MarthCage/FdD_Equipo_09/Proyecto/MóduloMecánico/Certificados ONSHAPE/Angel Valverde Paucarmayta/Certificados_Angel_Valverde_Paucarmayta.pdf

Onshape Fundamentals

April 28, 2026

Angel Valverde

Angel Valverde

April 28, 2026

Introduction to Drawings

Angel Valverde

Introduction to Part Studios

April 28, 2026

Angel Valverde

CAD Basics

April 28, 2026

Angel Valverde

Introduction to Sketching

April 28, 2026

Angel Valverde

April 28, 2026

Detailed Drawings

Angel Valverde

April 28, 2026

Introduction to Onshape Assemblies

Angel Gabriel Valverde Paucarmayta

Advanced Onshape Assemblies

May 19, 2026
