MarthCage/FdD_Equipo_09/Proyecto/MóduloMecánico/Certificados ONSHAPE/Martha Medina Rojas/Certificados_Martha_Medina_Rojas.pdf

Onshape Fundamentals

April 28, 2026

Martha Medina

Martha Medina

Introduction to Sketching

April 28, 2026

Martha Medina

Introduction to Part Studios

April 28, 2026

Martha Medina

CAD Basics

April 28, 2026

Martha Medina

April 28, 2026

Introduction to Drawings

Martha Medina

April 28, 2026

Detailed Drawings

Martha Medina

April 28, 2026

Introduction to Onshape Assemblies

Martha Medina

Advanced Onshape Assemblies

May 19, 2026
