MarthCage/FdD_Equipo_09/Recursos/Productos comerciales/Guardian 3.pdf

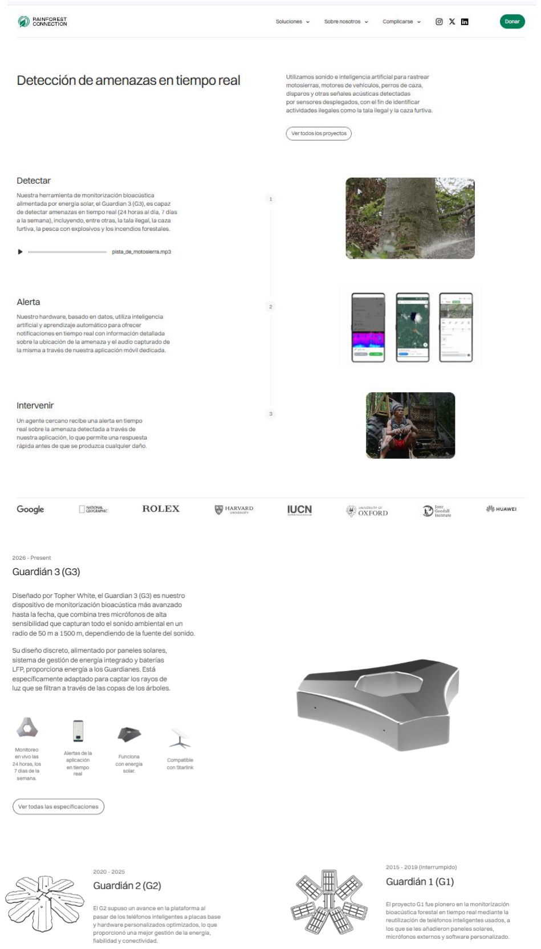
[picture p41: page 1]
