MarthCage/FdD_Equipo_09/Proyecto/MóduloElectrónico/V3.0/Esquemático 3.0 (2).pdf

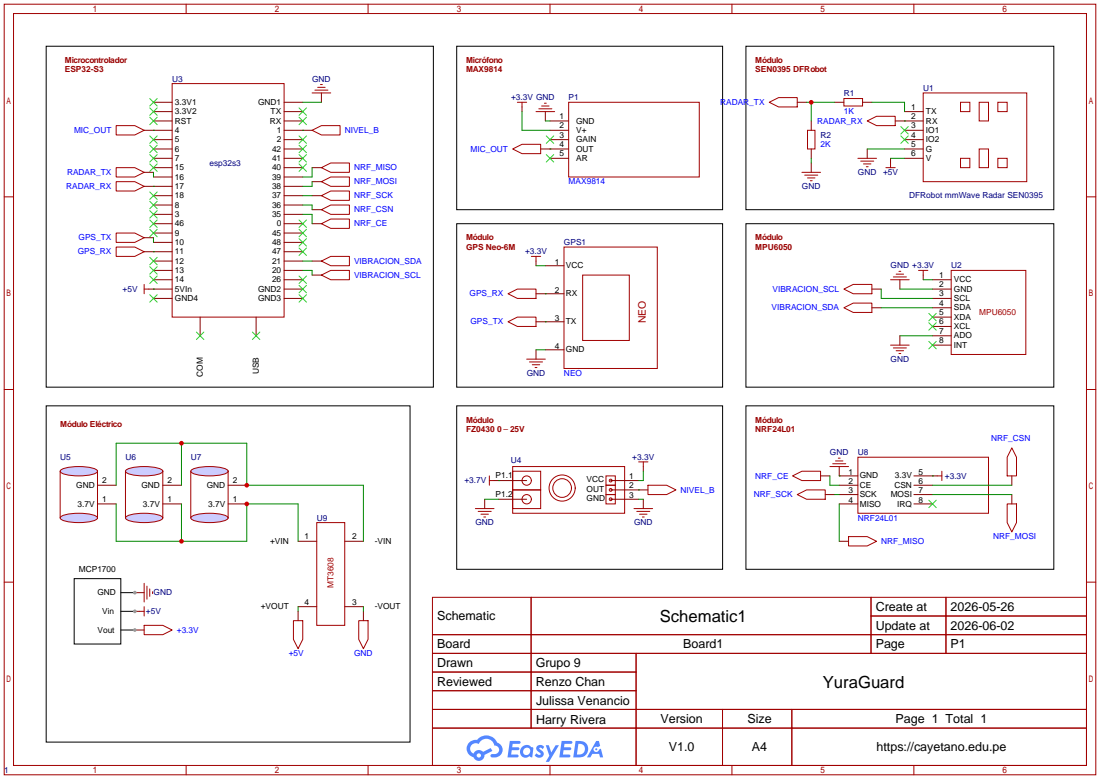
[picture p54: page 1]

Schematic | Schematic1 | Create at | 2026-05-26

Update at | 2026-06-02

Board | Board1 | Page | P1
Drawn | Grupo 9 | YuraGuard
Reviewed | Renzo Chan

Julissa Venancio
Harry Rivera | Version | Size | Page 1 Total 1

V1.0 | A4 | https://cayetano.edu.pe
