MarthCage/FdD_Equipo_09/Proyecto/MóduloMecánico/v2.0/Onshape/planos/PCB1_plano.pdf

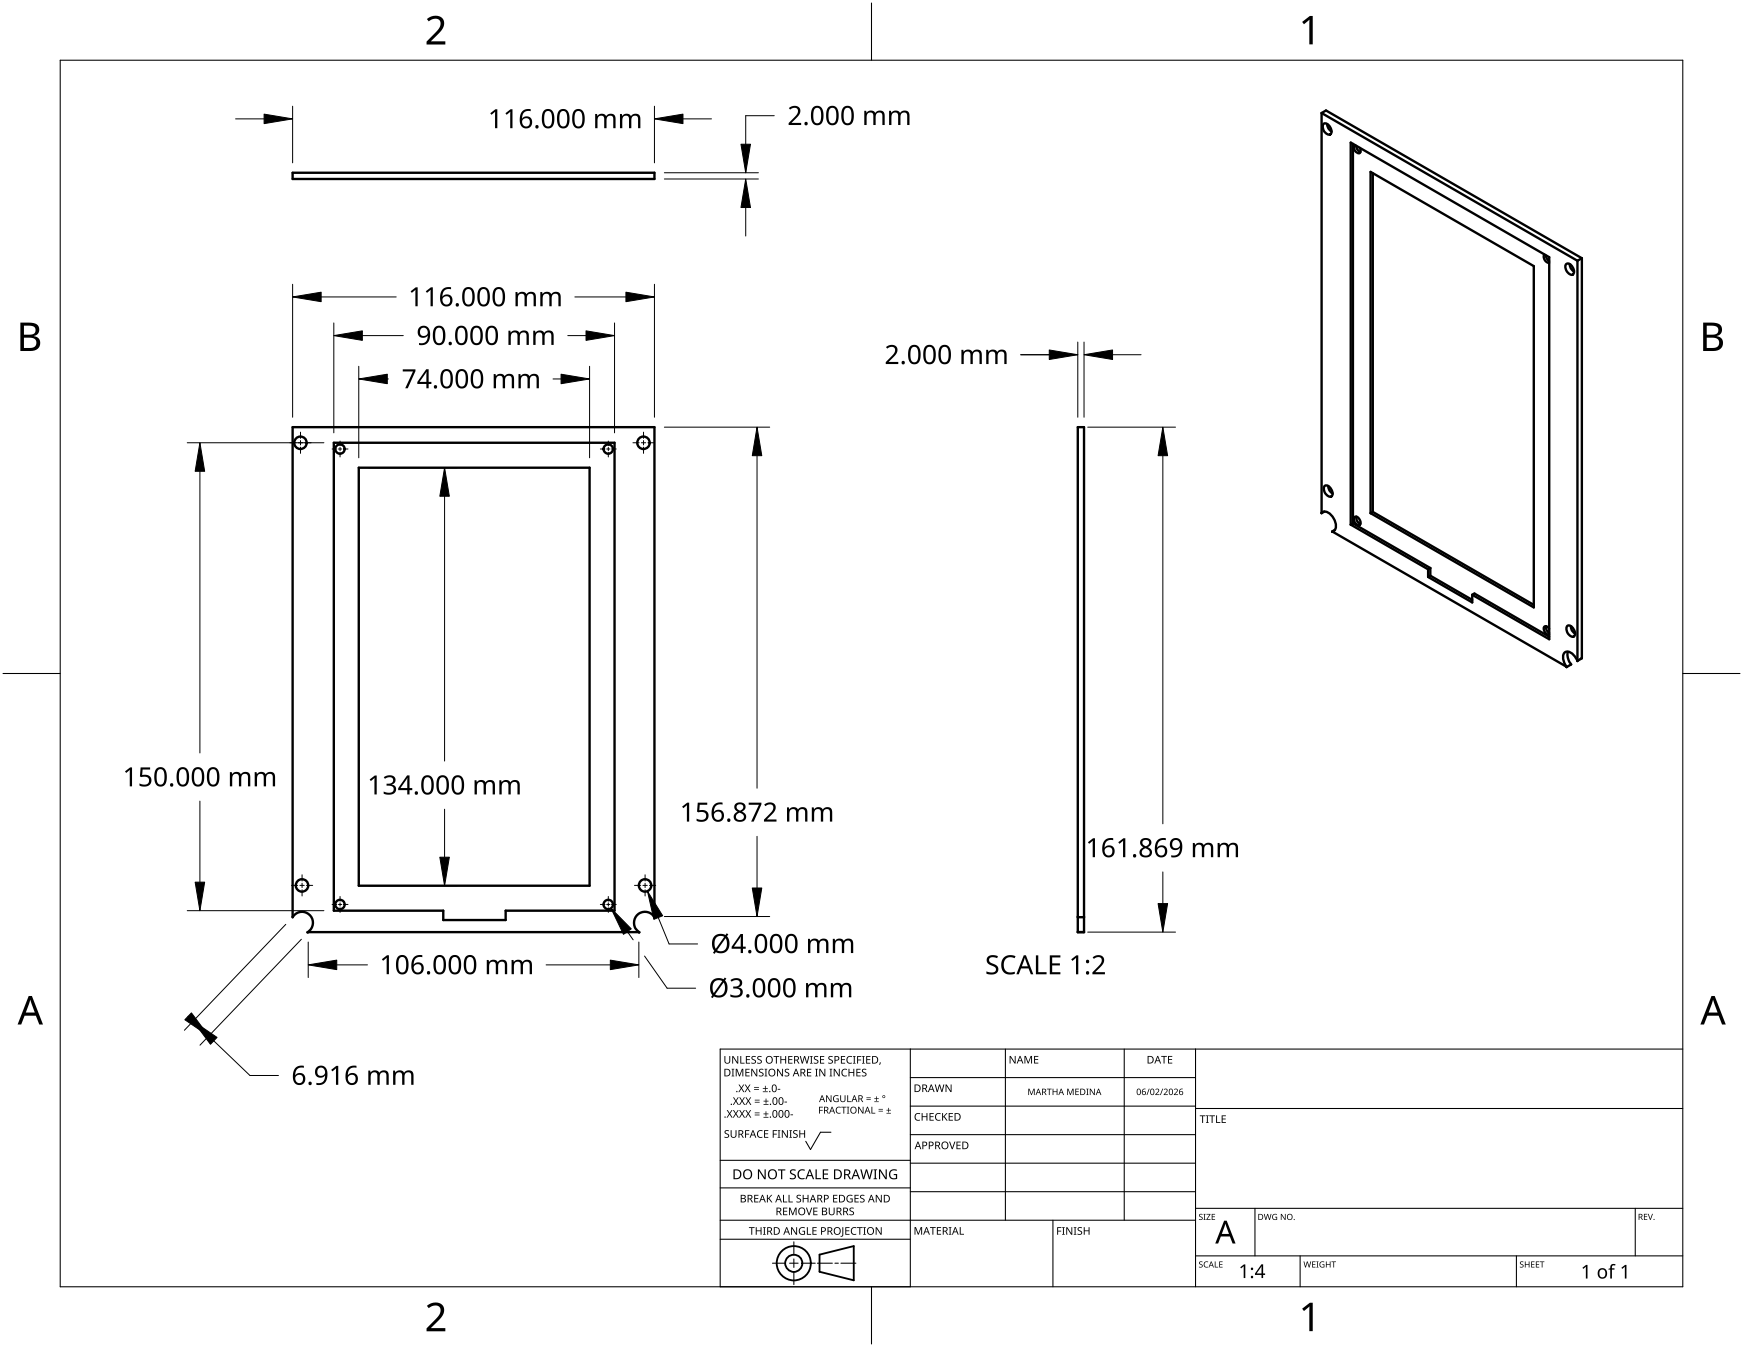
[picture p105: page 1]
