MarthCage/FdD_Equipo_09/Proyecto/MóduloMecánico/v2.0/Onshape/planos/PCB2_plano.pdf

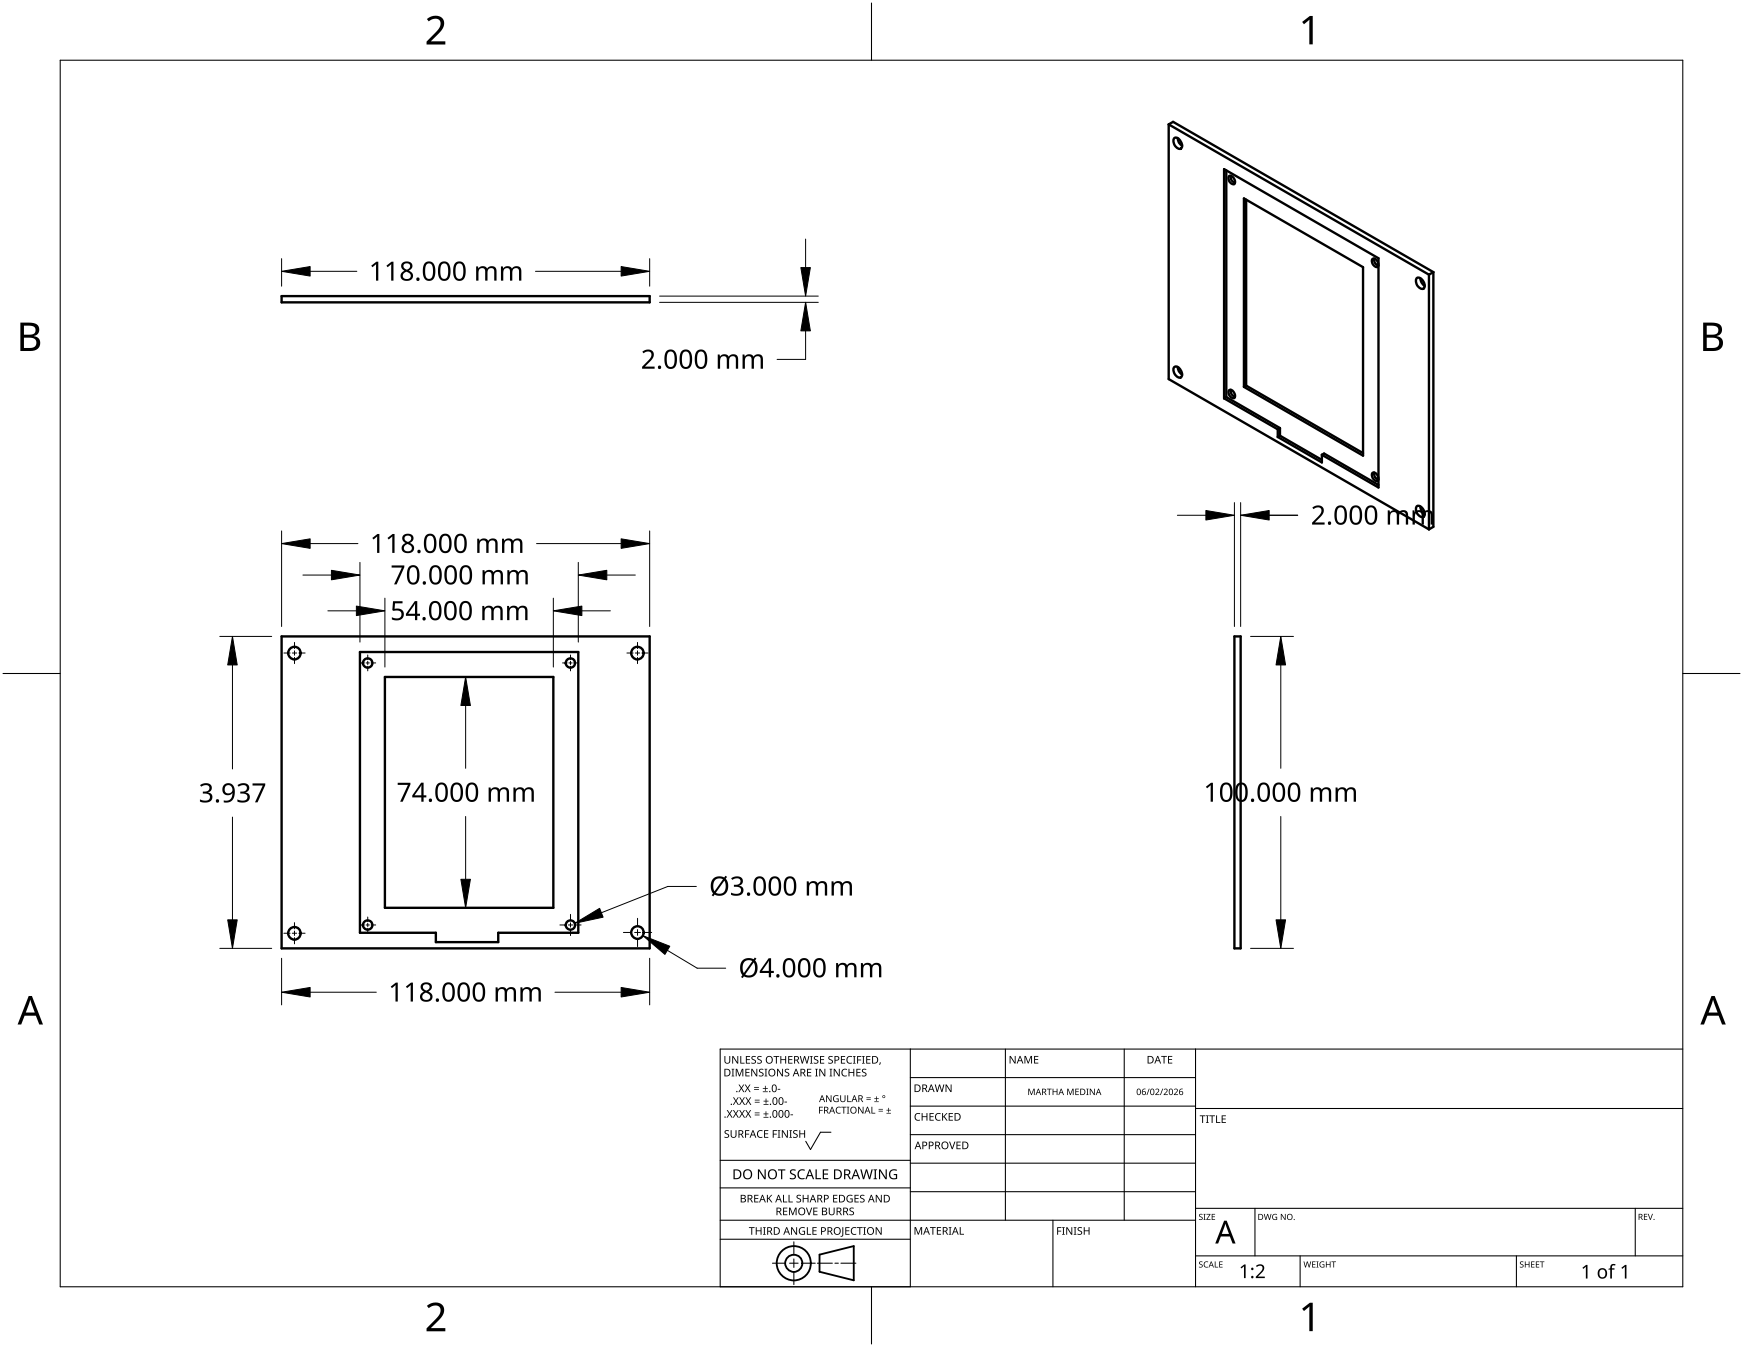
[picture p106: page 1]
