MarthCage/FdD_Equipo_09/Proyecto/MóduloMecánico/v2.0/Onshape/planos/Tapa_plano.pdf

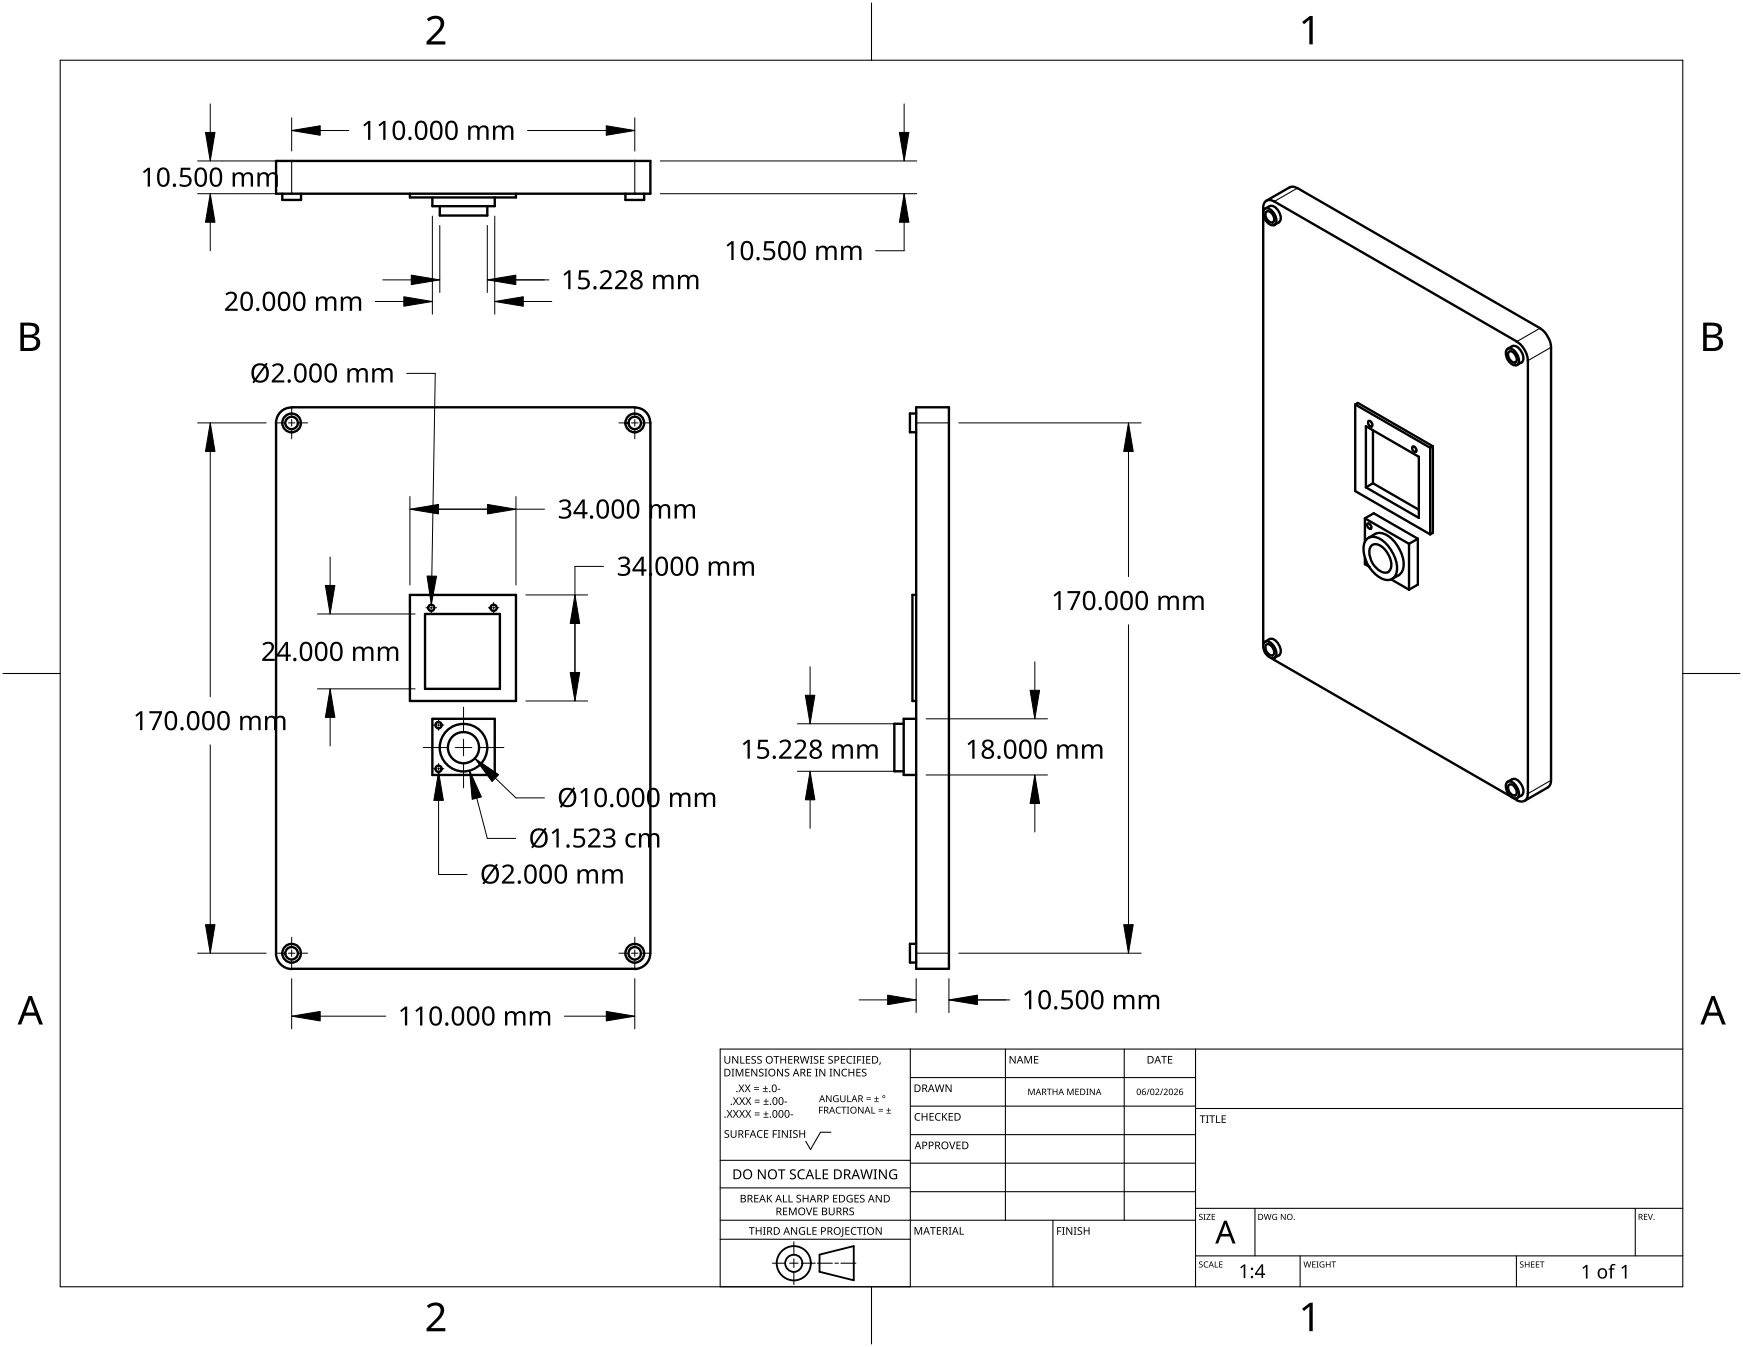
[picture p107: page 1]
