MarthCage/FdD_Equipo_09/Proyecto/MóduloElectrónico/V1.0/Esquemático 1.0.pdf

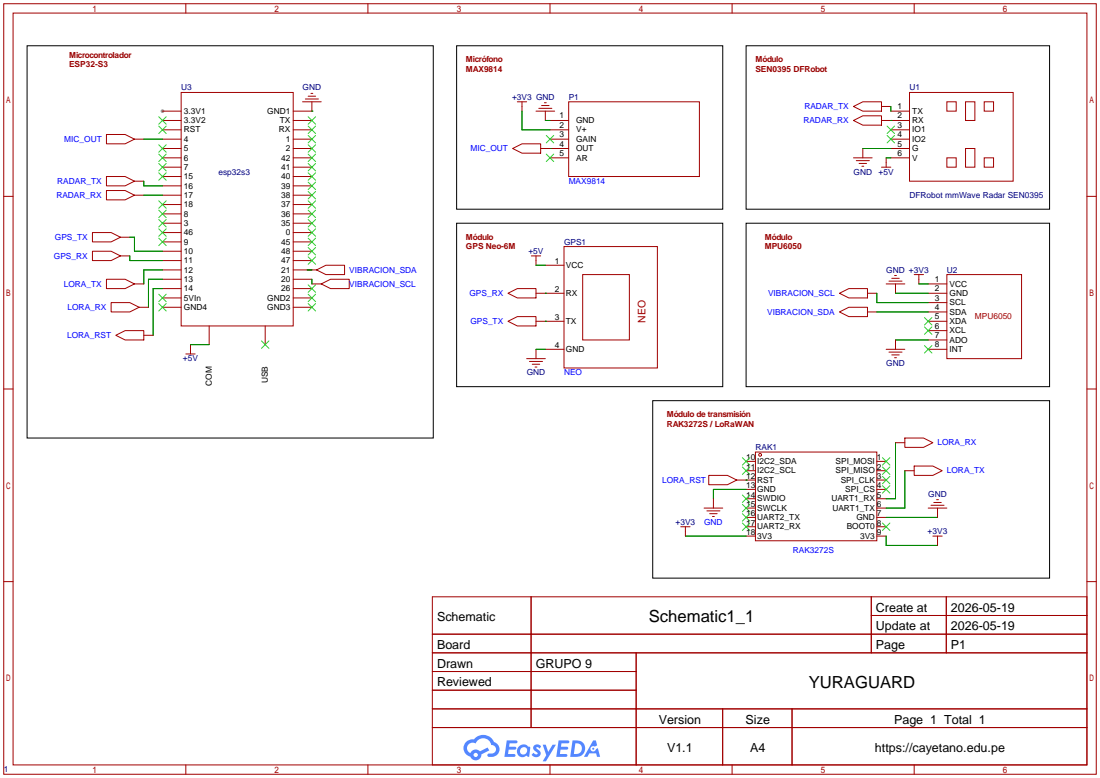
[picture p108: page 1]

Schematic | Schematic1_1 | Create at | 2026-05-19

Update at | 2026-05-19

Board | | Page | P1
Drawn | GRUPO 9 | YURAGUARD
Reviewed

Version | Size | Page 1 Total 1
V1.1 | A4 | https://cayetano.edu.pe
